Mic-Tsai/Sensor_ECG_PPG_MAX86150_Dev-Board/code/arduino/WiFi Transmission/ECG_PPG_MAX86150_V5_WiFi_RX/ESPNOW_RX.ino

/*
  Rui Santos
  Complete project details at https://RandomNerdTutorials.com/esp-now-esp8266-nodemcu-arduino-ide/
  
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
  The above copyright notice and this permission notice shall be included in all
  copies or substantial portions of the Software.
*/

#include <ESP8266WiFi.h>
#include <espnow.h>

// Structure example to receive data
// Must match the sender structure
typedef struct struct_message {
  int a;
  int b;
  int c;
  int d;
} struct_message;

// Create a struct_message called myData
struct_message myData;

// Callback function that will be executed when data is received
void OnDataRecv(uint8_t * mac, uint8_t *incomingData, uint8_t len) {
  memcpy(&myData, incomingData, sizeof(myData));

  /*
  Serial.print("Bytes received: ");
  Serial.println(len);
  Serial.print("Char: ");
  Serial.println(myData.a);
  Serial.print("Int: ");
  Serial.println(myData.b);
  Serial.print("Float: ");
  Serial.println(myData.c);
  Serial.print("String: ");
  Serial.println(myData.d);
  Serial.print("Bool: ");
  Serial.println(myData.e);
  Serial.println();
  */


  Serial.print(millis());
  Serial.print(",");
  Serial.print(myData.a - myData.b);
  Serial.print(",");
  Serial.print(myData.c - myData.d);
  Serial.println(",");
}
 
void setup() {
  // Initialize Serial Monitor
  Serial.begin(38400);
  
  // Set device as a Wi-Fi Station
  WiFi.mode(WIFI_STA);

  // Init ESP-NOW
  if (esp_now_init() != 0) {
    Serial.println("Error initializing ESP-NOW");
    return;
  }
  
  // Once ESPNow is successfully Init, we will register for recv CB to
  // get recv packer info
  esp_now_set_self_role(ESP_NOW_ROLE_SLAVE);
  esp_now_register_recv_cb(OnDataRecv);
}

void loop() {
  
}
